aavdiere/switched-calibration-kit/images/insertion-loss.png

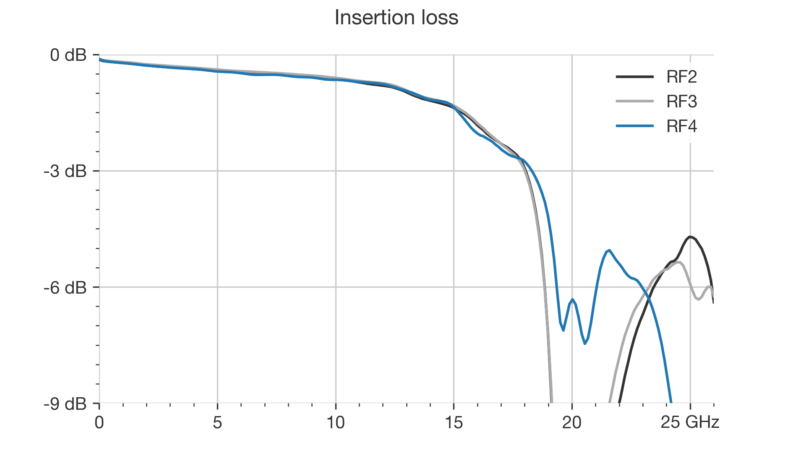
images/insertion-loss.png
